potatooooooooooooooo/Body-sensing-Mouse-Based-on-STM32-and-MPU6050/Attitude instrument/MDK-ARM/APP/commu.h

#ifndef __commu_H
#define __commu_H

#include "stdio.h"
#include "stdint.h"
#include "imu_data.h"
#include "math.h"
#include "stm32f1xx_hal.h"
#include "string.h"
#include "mavlink.h"
#include "imu_data.h"
#include "main.h"

extern UART_HandleTypeDef huart1;

void sent_data();
void data_process();


#endif
