potatooooooooooooooo/Body-sensing-Mouse-Based-on-STM32-and-MPU6050/Attitude instrument/MDK-ARM/DEVICE/OLED.h

#ifndef __OLED_H
#define __OLED_H
#include "stdint.h"
void OLED_Init(void);
void OLED_Clear(void);
void OLED_ShowChar(uint8_t Line, uint8_t Column, char Char);
void OLED_ShowString(uint8_t Line, uint8_t Column, char *String);
void OLED_ShowNum(uint8_t Line, uint8_t Column, uint32_t Number, uint8_t Length);
void OLED_ShowSignedNum(uint8_t Line, uint8_t Column, int32_t Number, uint8_t Length);
void OLED_ShowHexNum(uint8_t Line, uint8_t Column, uint32_t Number, uint8_t Length);
void OLED_ShowBinNum(uint8_t Line, uint8_t Column, uint32_t Number, uint8_t Length);
void OLED_Clear_Part(uint8_t Line, uint8_t start, uint8_t end);
void OLED_ShowWord(uint8_t Line, uint8_t Column, uint8_t Chinese);
void OLED_ShowChinese(uint8_t Line, uint8_t Column, uint8_t *Chinese,uint8_t Length);
void OLED_ShowFNum(uint8_t Line, uint8_t Column, float Number, uint8_t Length,uint8_t Flength);

#endif
